BIRDSOpenSource/BIRDS3-FAB/FAB_CAD/CN401.sldasm

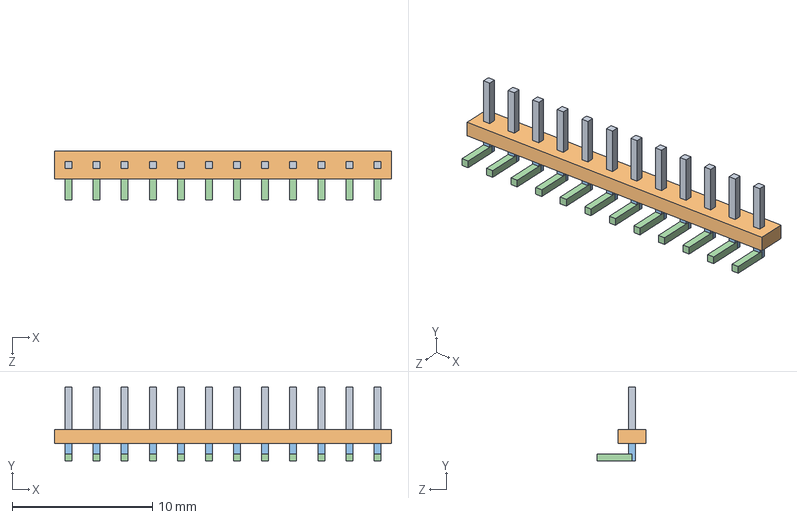
[picture p2: CAD file, 2021-10-05]
FAB_CAD/CN401.sldasm
24.0 x 5.25 x 3.50 mm
Extruded_17 x 12
Extruded_18
Extruded_19 x 12
Extruded_20 x 12
